JohnMarzulli/HangarBuddy/communication/meshtastic_serial.py

# T-Deck Plus requires a special process to flash
# https://www.om7tek.com/2025/how-to-flash-and-setup-meshtastic-with-ui-on-t-deck-plus/

# Installing tiles
# https://www.jeffgeerling.com/blog/2025/adding-gps-and-grid-maps-my-meshtastic-t-deck/

import time
from datetime import datetime, timezone

import meshtastic
import meshtastic.serial_interface
import serial.tools.list_ports
from pubsub import pub

if __name__ == "__main__":
    import os
    import sys

    # Ensure the parent directory is in sys.path so 'managers' can be imported
    # This is only needed if running the unit tests directly
    sys.path.append(os.path.abspath(os.path.join(os.path.dirname(__file__), "..")))

from communication.message_send_request import MessageSendRequest
from communication.received_message import ReceivedMessage
from devices.interfaces.messaging_device import MessagingDevice
from lib.system_level_logging import SystemLevelLogger


class MeshtasticSerial(MessagingDevice):
    def __init__(self, logger: SystemLevelLogger):
        super().__init__(logger)
        self.__meshastic_interface__: meshtastic.serial_interface.SerialInterface | None = None

    def __is_device_allocated__(self) -> bool:
        return self.__meshastic_interface__ is not None

    async def __receive_message__(self) -> bool:
        return False

    async def __send_single_message__(self, request: MessageSendRequest):
        if not self.__meshastic_interface__:
            return False
        try:
            self.__meshastic_interface__.sendText(request.text, destinationId=request.recipient)

            return True
        except Exception as e:
            return False

    def __is_connected__(self) -> bool:
        """
        Check if the Meshtastic device is connected.
        """
        is_connected: bool = (
            self.__meshastic_interface__ is not None and self.__meshastic_interface__.isConnected.is_set()
        )

        return is_connected

    async def __reconnect__(self):
        """
        Close the connection to the Meshtastic device.
        """
        if hasattr(self, "meshastic_interface") and self.__meshastic_interface__ is not None:
            self.__meshastic_interface__.close()

        self.__meshastic_interface__ = self.__connect_to_device__()
        self.device_name = str(self.__meshastic_interface__.getShortName())
        self.device_id = f"!{hex(self.__meshastic_interface__.myInfo.my_node_num).replace('0x', '')}"  # type: ignore
        pub.subscribe(self.__on_receive__, "meshtastic.receive")

    def __connect_to_device__(self) -> meshtastic.serial_interface.SerialInterface:
        all_ports = serial.tools.list_ports.comports()
        ports = [port.device for port in all_ports]

        for port in ports:
            self.__logger__.info(f"Trying to connect to Meshtastic device on {port}...")

            try:
                potential_meshastic_interface = meshtastic.serial_interface.SerialInterface(devPath=port)
                # Wait for node info to confirm connection
                time.sleep(2)
                if potential_meshastic_interface.myInfo:
                    self.__logger__.info(f"Connected to Meshtastic device on {port}.")

                    return potential_meshastic_interface
            except Exception as ex:
                self.__logger__.error(f"While attempting connection to Meshtastic on {port}, EX={ex}")
                continue
        raise ConnectionError("No Meshtastic device found on any serial port, or all the devices is already connected.")

    def __on_receive__(self, packet, interface):
        try:
            # Only queue messages intended for this device
            if packet is not None and "decoded" in packet and packet["decoded"]["portnum"] == "TEXT_MESSAGE_APP":
                sender: str = packet["fromId"]
                recipient: str = packet["toId"]
                text: str = packet["decoded"]["payload"].decode("utf-8")
                # Packets do not seem to have a timestamp
                time_received: datetime = datetime.now(tz=timezone.utc)
                incoming_message: ReceivedMessage = ReceivedMessage(time_received, sender, recipient, text)
                self.__receiving_queue__.append(incoming_message)
        except KeyError as e:
            self.__logger__.error(f"Error processing packet: {e}")


if __name__ == "__main__":
    import asyncio

    from configuration import Configuration
    from devices.interfaces.messaging_device import test_loop
    from lib.system_level_logging import SystemLevelLogger

    meshtastic_device: MeshtasticSerial = MeshtasticSerial(SystemLevelLogger(Configuration(), "MeshtasticSerialTester"))
    recipient = "!ba66ffe4"

    asyncio.run(test_loop(meshtastic_device, recipient))
