JohnMarzulli/HangarBuddy/devices/simulated_gas_sensor.py

"""Module to simulate the gas sensor."""

from devices.gas_sensor import GasSensor
from devices.gas_sensor_result import GasSensorResult
from devices.sensor_simulator import SensorSimulator

DEFAULT_TRIGGER_THRESHOLD = 245
DEFAULT_ALL_CLEAR_THRESHOLD = 235


class SimulatedGasSensor(GasSensor):
    """
    Simulates a gas sensor for testing purposes.
    """

    def __init__(
        self,
        sensor_trigger_threshold=DEFAULT_TRIGGER_THRESHOLD,
        sensor_all_clear_threshold=DEFAULT_ALL_CLEAR_THRESHOLD,
    ):
        super().__init__(sensor_trigger_threshold, sensor_all_clear_threshold)

        print("Starting init")

        self.enabled = True
        self.is_gas_detected = False
        self.sensor_trigger_threshold = sensor_trigger_threshold
        self.sensor_all_clear_threshold = sensor_all_clear_threshold
        self.__sensor_simulator__: SensorSimulator = SensorSimulator(
            sensor_all_clear_threshold * 0.8, sensor_trigger_threshold * 1.1, 5
        )
        self.current_value = int(self.__sensor_simulator__.get_current_value())

    def update(self):
        """
        Simulates an I2C based MQ2 gas sensor reading.
        """

        self.current_value = int(self.__sensor_simulator__.read())

        self.is_gas_detected = self.current_value > self.sensor_all_clear_threshold

        return GasSensorResult(self.is_gas_detected, self.current_value)
